aoi2010/AOILED/Firmware/WLED-0.15.3/images/macbook-pro-space-gray-on-the-wooden-table.jpg

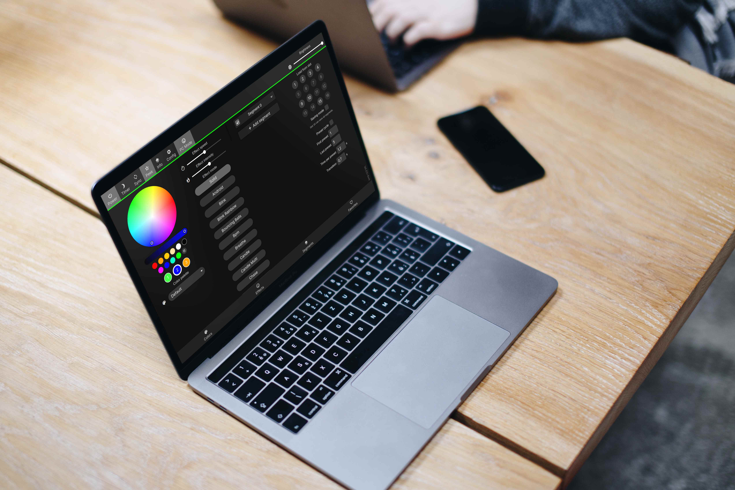
Firmware/WLED-0.15.3/images/macbook-pro-space-gray-on-the-wooden-table.jpg
