aoi2010/AOILED/Firmware/WLED-0.15.3/images/walking-with-iphone-x.jpg

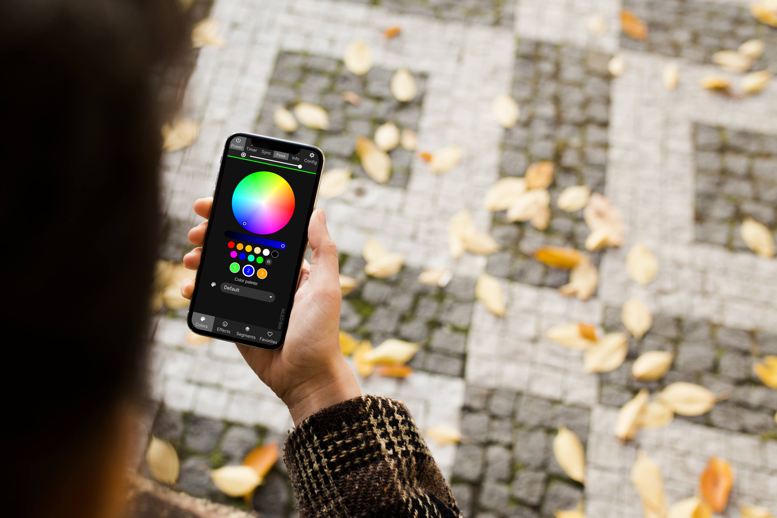
Firmware/WLED-0.15.3/images/walking-with-iphone-x.jpg
