aoi2010/AOILED/Firmware/WLED-0.15.3/usermods/Battery/assets/battery_connection_schematic_02.png

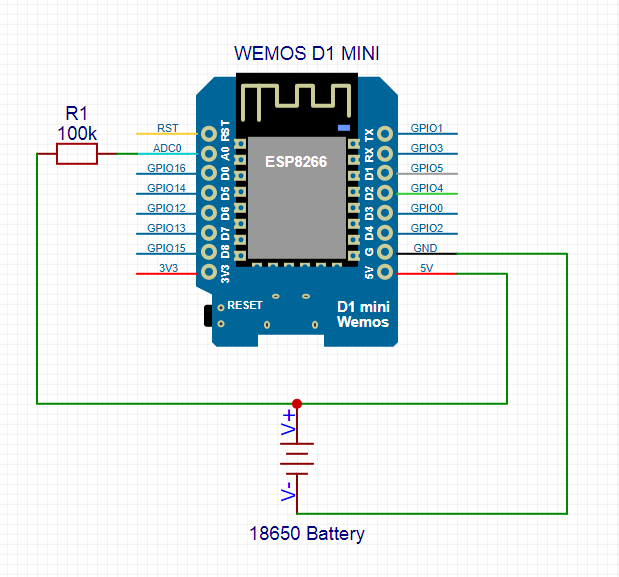
Firmware/WLED-0.15.3/usermods/Battery/assets/battery_connection_schematic_02.png
