aoi2010/AOILED/Firmware/WLED-0.15.3/usermods/Battery/assets/battery_connection_schematic_esp32.png

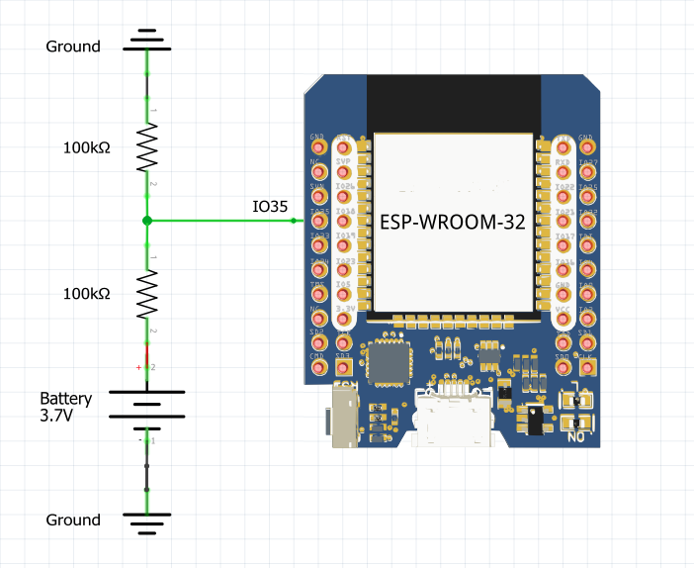
Firmware/WLED-0.15.3/usermods/Battery/assets/battery_connection_schematic_esp32.png
