aoi2010/AOILED/Firmware/WLED-0.15.3/usermods/Battery/assets/battery_connection_schematic_esp32_v2.png

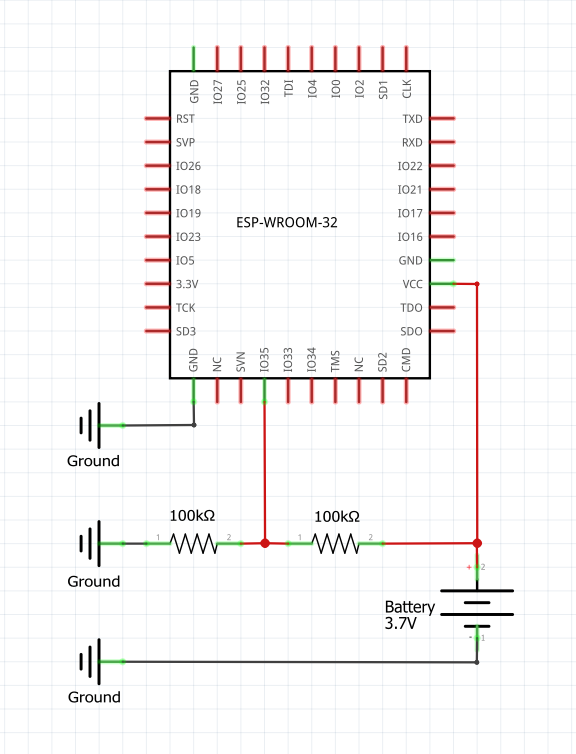
Firmware/WLED-0.15.3/usermods/Battery/assets/battery_connection_schematic_esp32_v2.png
