aoi2010/AOILED/Firmware/WLED-0.15.3/usermods/Battery/assets/battery_info_screen.png

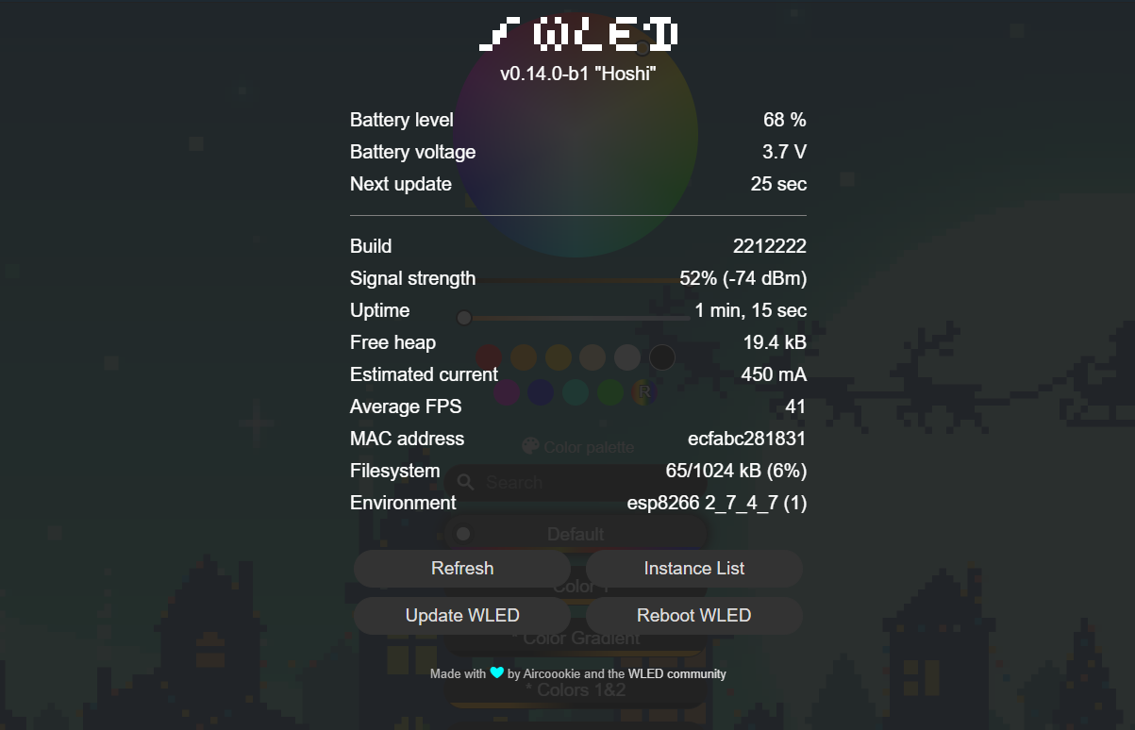
Firmware/WLED-0.15.3/usermods/Battery/assets/battery_info_screen.png
