aoi2010/AOILED/Firmware/WLED-0.15.3/usermods/battery_keypad_controller/assets/bat-key-ctrl-3.jpg

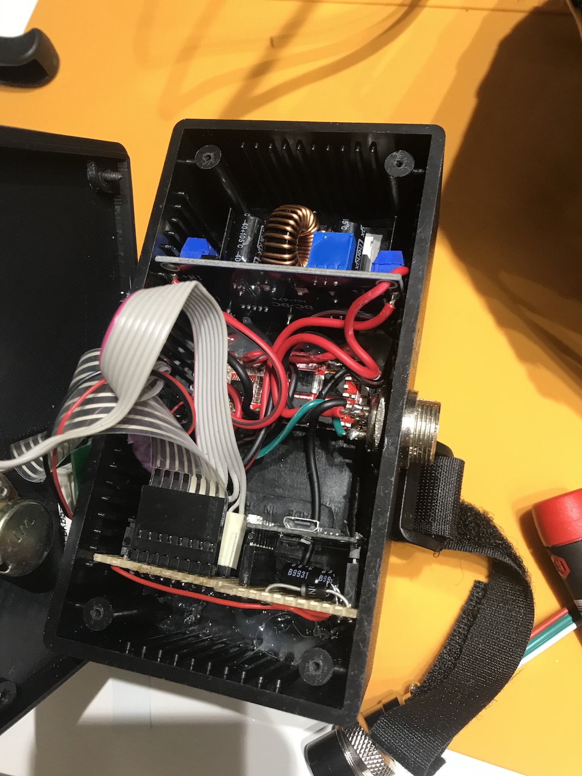
Firmware/WLED-0.15.3/usermods/battery_keypad_controller/assets/bat-key-ctrl-3.jpg
