aoi2010/AOILED/Firmware/WLED-0.15.3/usermods/BME68X_v2/pics/pic6.png

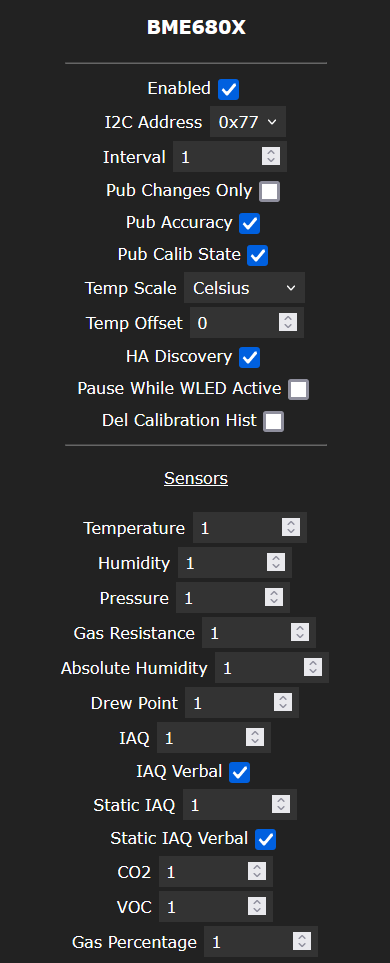
Firmware/WLED-0.15.3/usermods/BME68X_v2/pics/pic6.png
