aoi2010/AOILED/Firmware/WLED-0.15.3/usermods/Enclosure_with_OLED_temp_ESP07/assets/controller.jpg

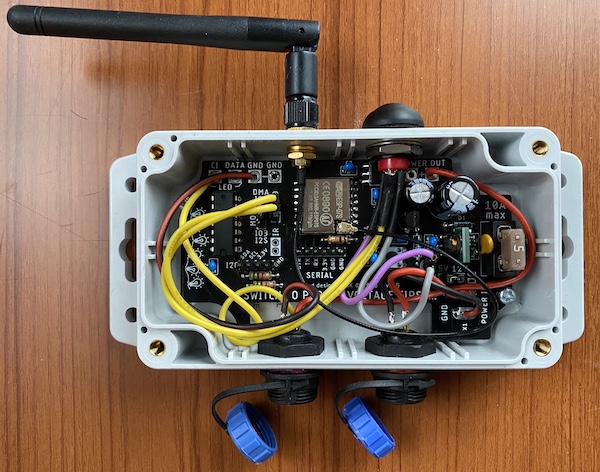
Firmware/WLED-0.15.3/usermods/Enclosure_with_OLED_temp_ESP07/assets/controller.jpg
