aoi2010/AOILED/Firmware/WLED-0.15.3/usermods/Internal_Temperature_v2/assets/screenshot_info.png

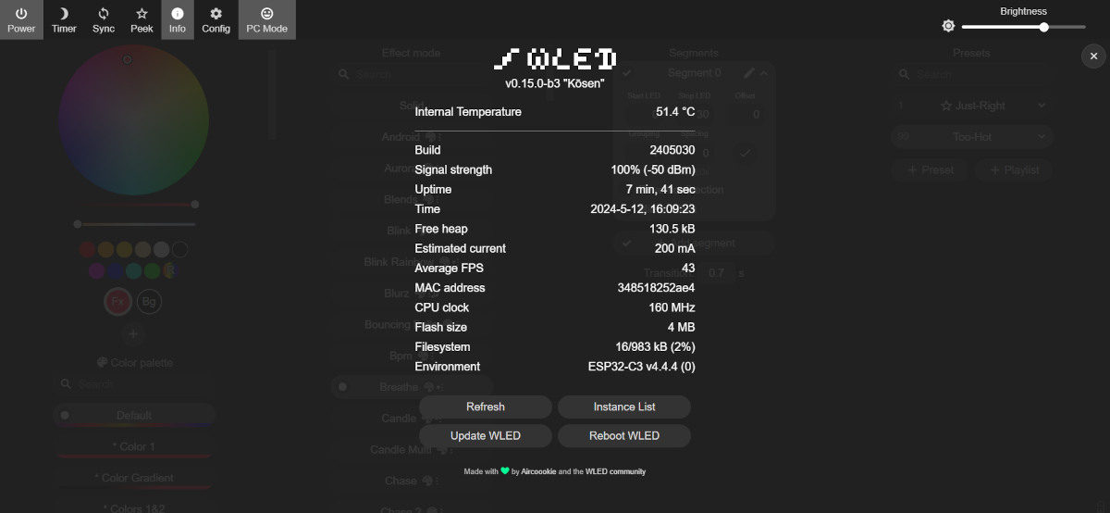
Firmware/WLED-0.15.3/usermods/Internal_Temperature_v2/assets/screenshot_info.png
