aoi2010/AOILED/Firmware/WLED-0.15.3/usermods/Internal_Temperature_v2/assets/screenshot_settings.png

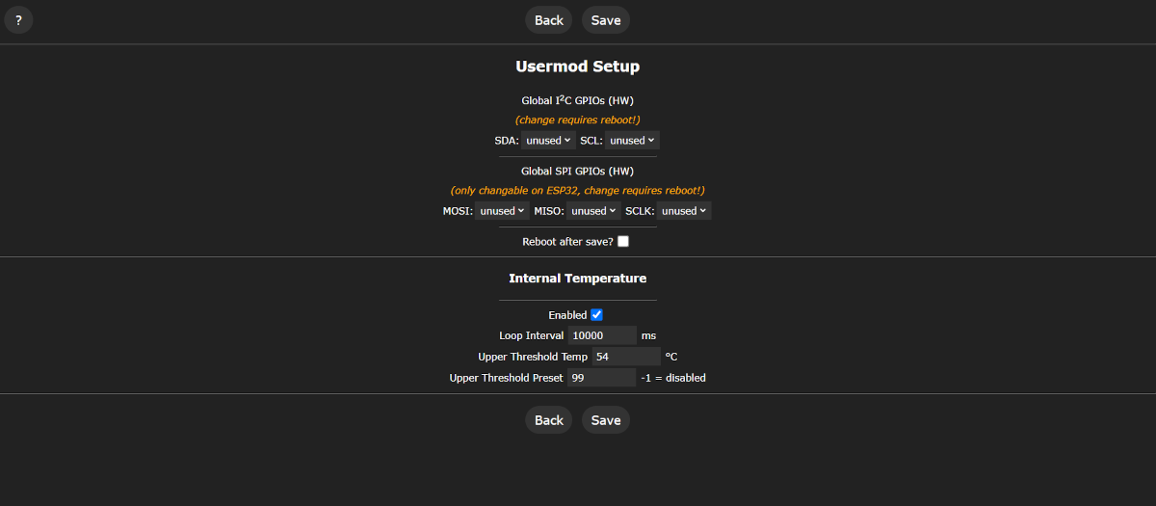
Firmware/WLED-0.15.3/usermods/Internal_Temperature_v2/assets/screenshot_settings.png
