aoi2010/AOILED/Firmware/WLED-0.15.3/usermods/pixels_dice_tray/images/roll_plot.png

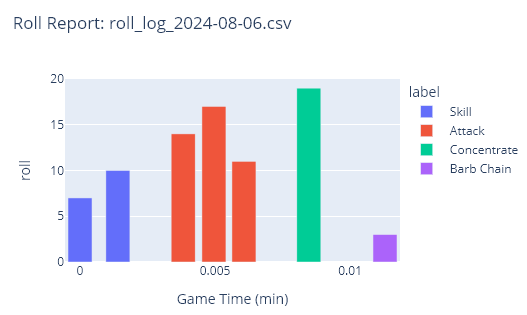
Firmware/WLED-0.15.3/usermods/pixels_dice_tray/images/roll_plot.png
