aoi2010/AOILED/Firmware/WLED-0.15.3/usermods/pixels_dice_tray/images/status.webp

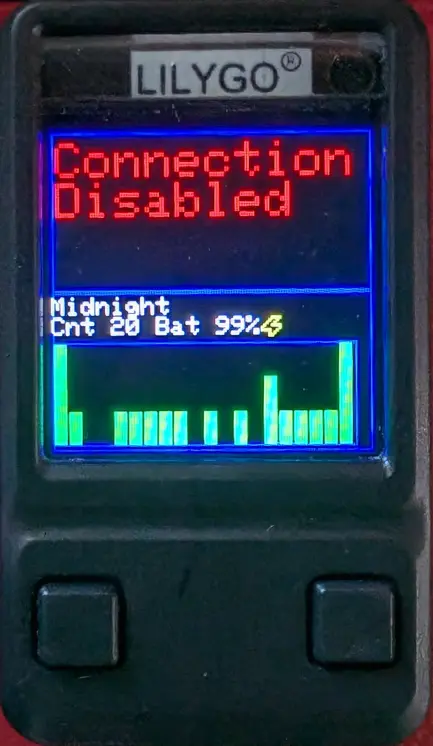
Firmware/WLED-0.15.3/usermods/pixels_dice_tray/images/status.webp
