aoi2010/AOILED/Firmware/WLED-0.15.3/usermods/TTGO-T-Display/assets/ttgo-tdisplay-enclosure1a.png

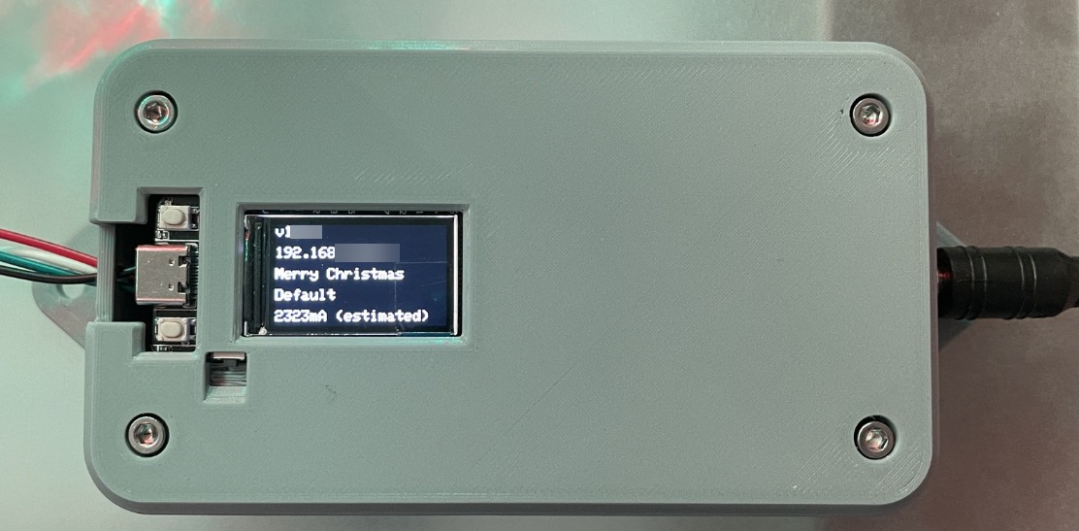
Firmware/WLED-0.15.3/usermods/TTGO-T-Display/assets/ttgo-tdisplay-enclosure1a.png
