aoi2010/AOILED/Firmware/WLED-0.15.3/usermods/Battery/assets/installation_my_config_h.png

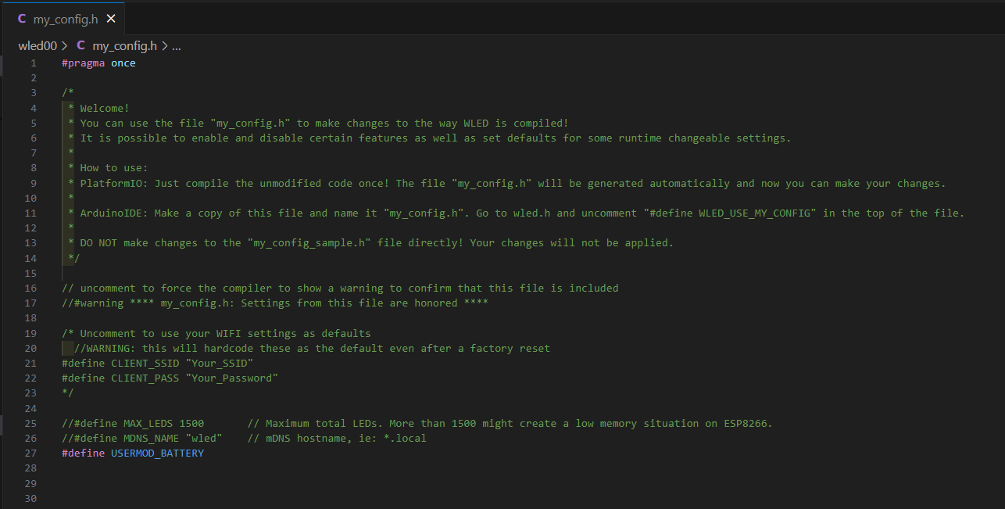
Firmware/WLED-0.15.3/usermods/Battery/assets/installation_my_config_h.png
