aoi2010/AOILED/Firmware/WLED-0.15.3/usermods/Battery/assets/installation_platformio_override_ini.png

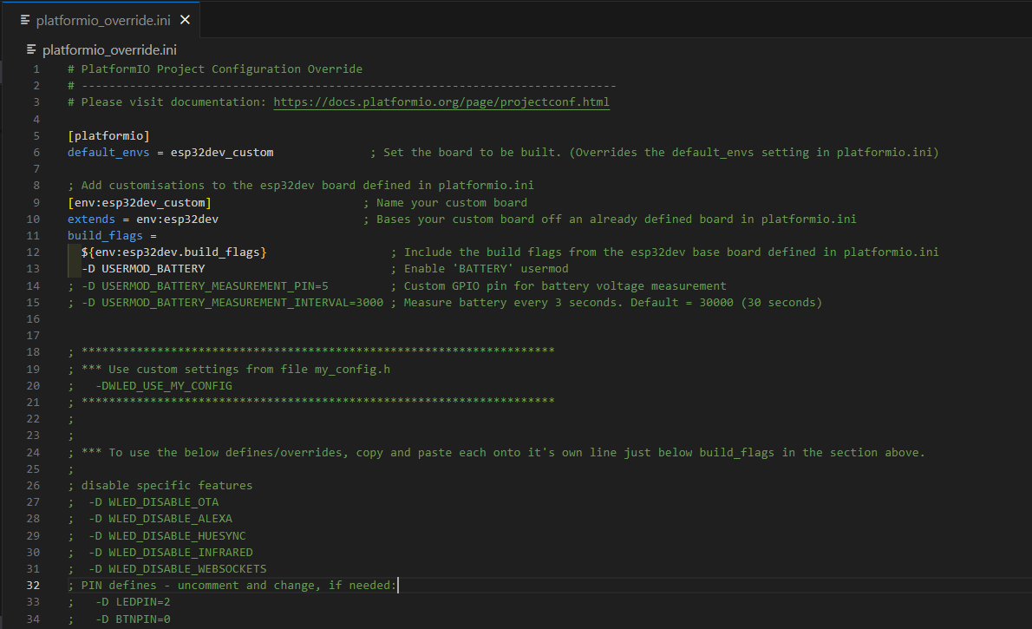
Firmware/WLED-0.15.3/usermods/Battery/assets/installation_platformio_override_ini.png
