aoi2010/AOILED/Firmware/WLED-0.15.3/usermods/ST7789_display/images/ST7789_Guide.jpg

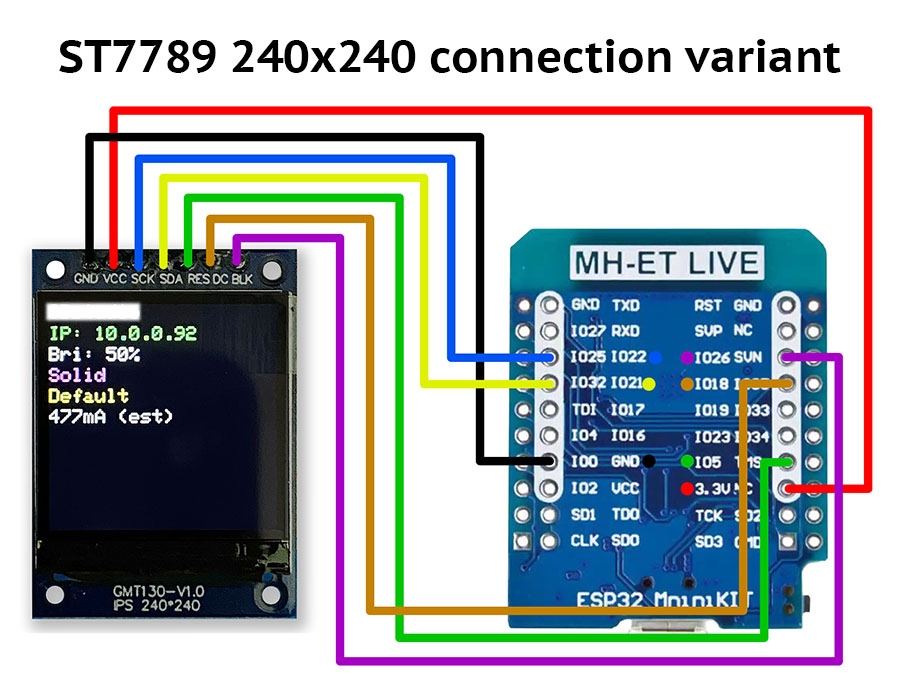
Firmware/WLED-0.15.3/usermods/ST7789_display/images/ST7789_Guide.jpg
